kwikius/aerflite/docs/flightDimension.png

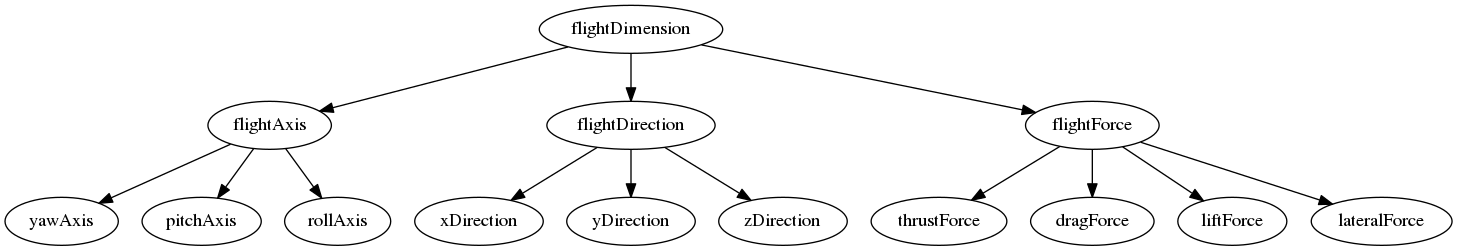
docs/flightDimension.png
